ManBearPigWolf/FLAB-Putter/FLAB Putter/STEP files/Soft Jaws A.STEP

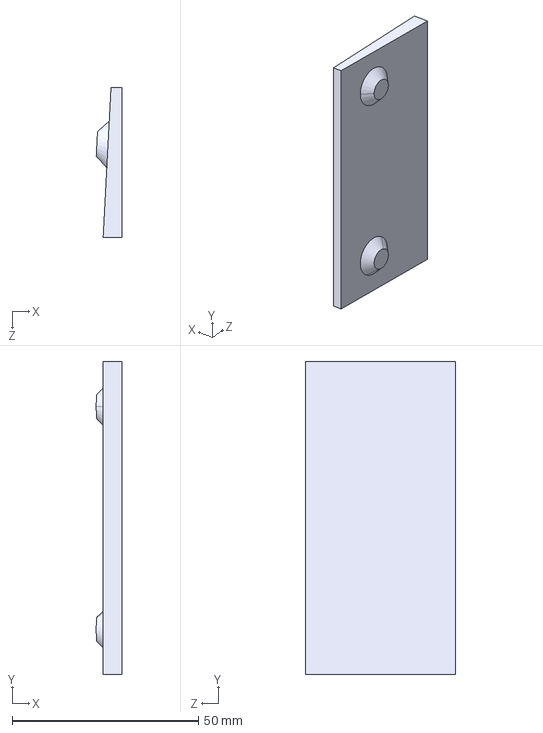
[picture p14: CAD file, 2025-06-18]
FLAB Putter/STEP files/Soft Jaws A.STEP
6.86 x 84.0 x 40.1 mm
