ManBearPigWolf/FLAB-Putter/Little FLAB Putter/Stability Shaft.SLDPRT

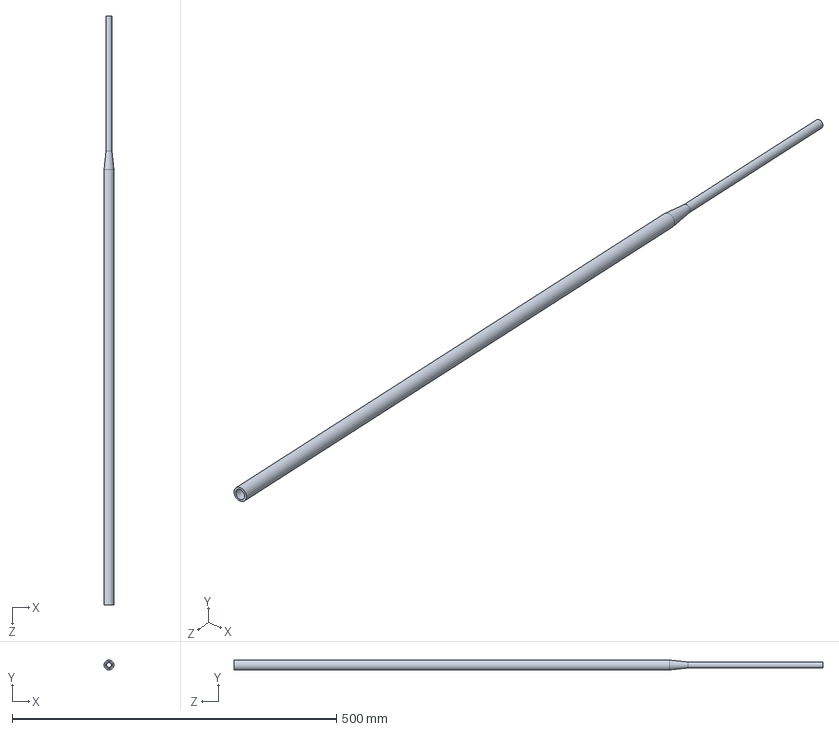
[picture p15: CAD file, 2025-06-18]
Little FLAB Putter/Stability Shaft.SLDPRT
15.2 x 15.2 x 908.0 mm
