ManBearPigWolf/FLAB-Putter/Little FLAB Putter/weight.SLDPRT

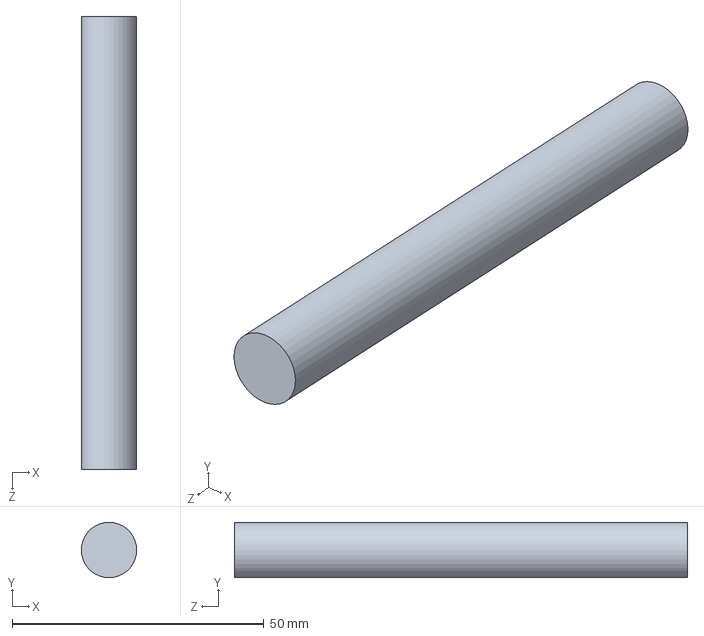
[picture p16: CAD file, 2025-06-18]
Little FLAB Putter/weight.SLDPRT
11.0 x 11.0 x 90.0 mm
