ManBearPigWolf/FLAB-Putter/Little FLAB Putter/STEP files/Little FLAB.STEP

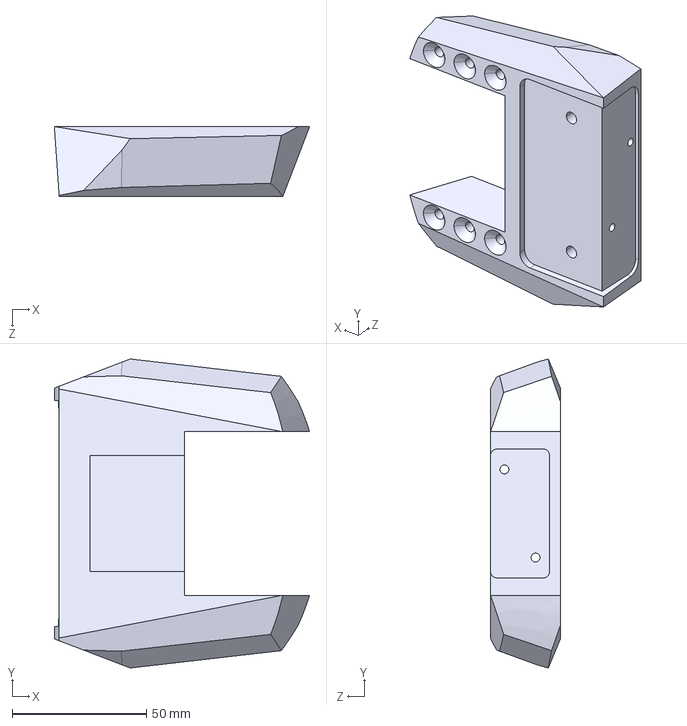
[picture p17: CAD file, 2025-06-27]
Little FLAB Putter/STEP files/Little FLAB.STEP
95.0 x 114.9 x 26.0 mm
